dvystrcil/neptune/configuration/pre-open-neptune/adxlmcu.cfg

[mcu adxl]
serial: /dev/serial/by-id/usb-Anchor_Rampon-if00

[adxl345]
cs_pin: adxl:CS
#cs_pin: adxl:gpio1

# Hardware SPI Option (Better results, "Invalid ID" Klipper bug with first query)
#spi_bus: spi0a

[resonance_tester]
accel_chip: adxl345
probe_points:
   112.5,112.5,20
# Edit the above line with the correct probe points location. I recommend the center of your bed for X & Y, 20 for Z.
# For 350 mm printers: 175,175,20
# For 300 mm printers: 150,150,20
# For 250 mm printers: 125,125,20
# For 120 mm printers: 60,60,20

# More info: https://www.klipper3d.org/Config_Reference.html#adxl345
